TanujRai14/Rf_pcb/Screenshot 2025-09-06 205506.png

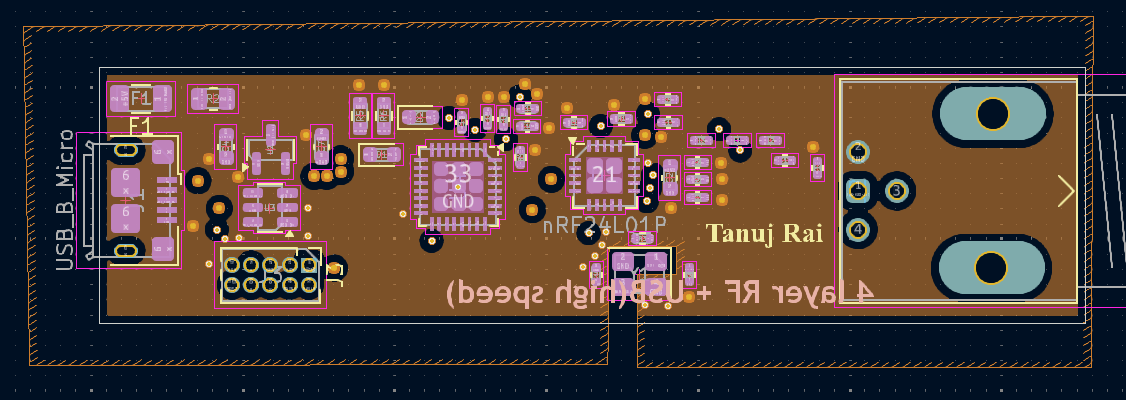
Screenshot 2025-09-06 205506.png
